SudoQTR-WRO2025/WRO2025_Robot/docs/images/back.jpg

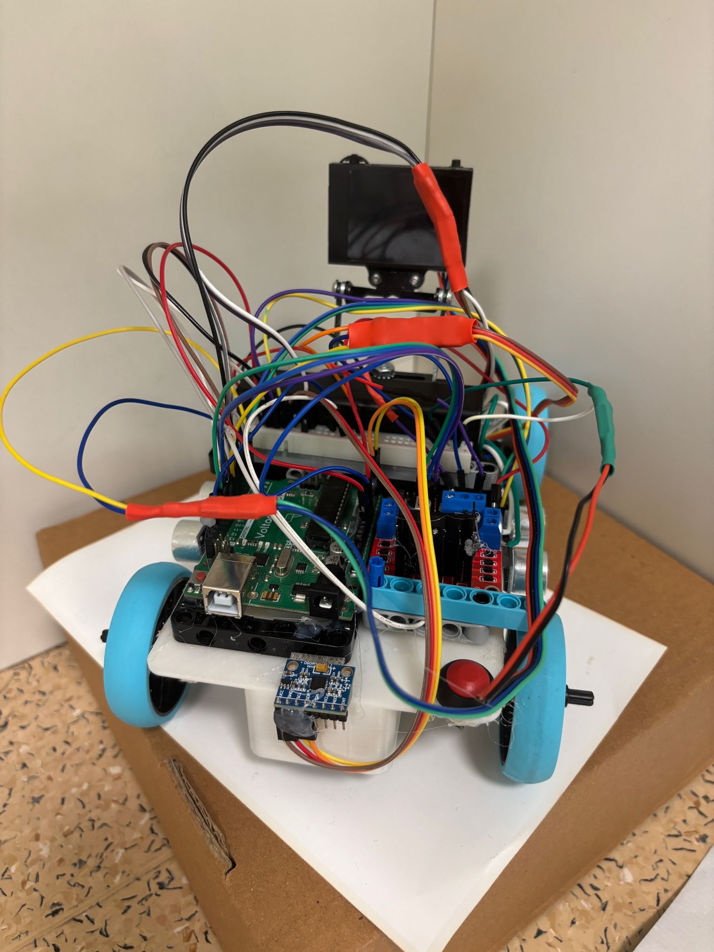
docs/images/back.jpg
