SudoQTR-WRO2025/WRO2025_Robot/docs/images/front.jpg

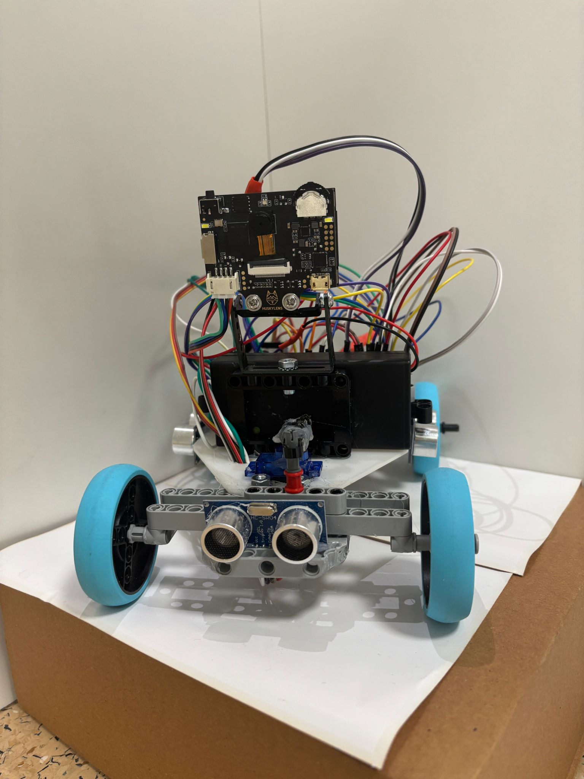
docs/images/front.jpg
