SudoQTR-WRO2025/WRO2025_Robot/team/AhmedOsama_Programmer.jpg

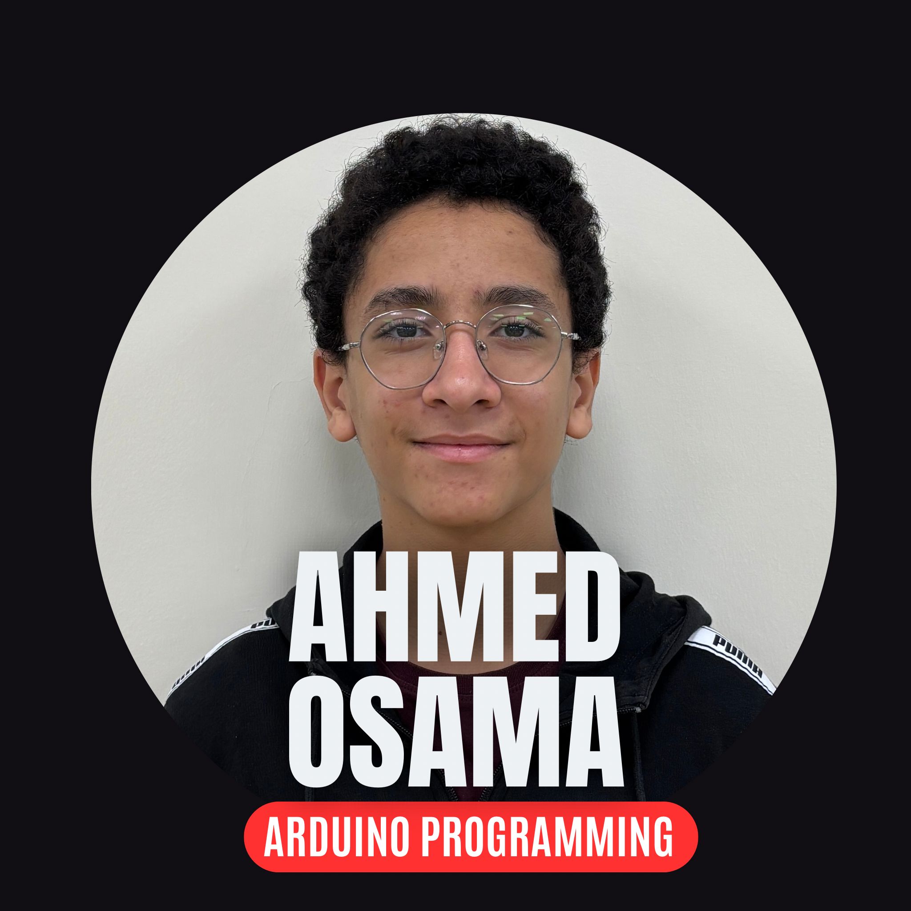
team/AhmedOsama_Programmer.jpg
