SudoQTR-WRO2025/WRO2025_Robot/team/NasserHassan_Testing.jpg

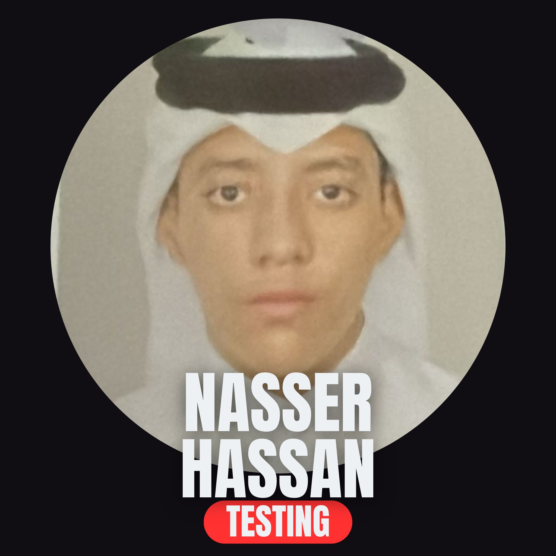
team/NasserHassan_Testing.jpg
